ProjectFishWorks/BaseStation/Firmware/BaseStation/src/credential.h

const char* CA_cert = \
"-----BEGIN CERTIFICATE-----\n" \ 
"MIIFazCCA1OgAwIBAgIRAIIQz7DSQONZRGPgu2OCiwAwDQYJKoZIhvcNAQELBQAw\n" \
"TzELMAkGA1UEBhMCVVMxKTAnBgNVBAoTIEludGVybmV0IFNlY3VyaXR5IFJlc2Vh\n" \
"cmNoIEdyb3VwMRUwEwYDVQQDEwxJU1JHIFJvb3QgWDEwHhcNMTUwNjA0MTEwNDM4\n" \
"WhcNMzUwNjA0MTEwNDM4WjBPMQswCQYDVQQGEwJVUzEpMCcGA1UEChMgSW50ZXJu\n" \
"ZXQgU2VjdXJpdHkgUmVzZWFyY2ggR3JvdXAxFTATBgNVBAMTDElTUkcgUm9vdCBY\n" \
"MTCCAiIwDQYJKoZIhvcNAQEBBQADggIPADCCAgoCggIBAK3oJHP0FDfzm54rVygc\n" \
"h77ct984kIxuPOZXoHj3dcKi/vVqbvYATyjb3miGbESTtrFj/RQSa78f0uoxmyF+\n" \
"0TM8ukj13Xnfs7j/EvEhmkvBioZxaUpmZmyPfjxwv60pIgbz5MDmgK7iS4+3mX6U\n" \
"A5/TR5d8mUgjU+g4rk8Kb4Mu0UlXjIB0ttov0DiNewNwIRt18jA8+o+u3dpjq+sW\n" \
"T8KOEUt+zwvo/7V3LvSye0rgTBIlDHCNAymg4VMk7BPZ7hm/ELNKjD+Jo2FR3qyH\n" \
"B5T0Y3HsLuJvW5iB4YlcNHlsdu87kGJ55tukmi8mxdAQ4Q7e2RCOFvu396j3x+UC\n" \
"B5iPNgiV5+I3lg02dZ77DnKxHZu8A/lJBdiB3QW0KtZB6awBdpUKD9jf1b0SHzUv\n" \
"KBds0pjBqAlkd25HN7rOrFleaJ1/ctaJxQZBKT5ZPt0m9STJEadao0xAH0ahmbWn\n" \
"OlFuhjuefXKnEgV4We0+UXgVCwOPjdAvBbI+e0ocS3MFEvzG6uBQE3xDk3SzynTn\n" \
"jh8BCNAw1FtxNrQHusEwMFxIt4I7mKZ9YIqioymCzLq9gwQbooMDQaHWBfEbwrbw\n" \
"qHyGO0aoSCqI3Haadr8faqU9GY/rOPNk3sgrDQoo//fb4hVC1CLQJ13hef4Y53CI\n" \
"rU7m2Ys6xt0nUW7/vGT1M0NPAgMBAAGjQjBAMA4GA1UdDwEB/wQEAwIBBjAPBgNV\n" \
"HRMBAf8EBTADAQH/MB0GA1UdDgQWBBR5tFnme7bl5AFzgAiIyBpY9umbbjANBgkq\n" \
"hkiG9w0BAQsFAAOCAgEAVR9YqbyyqFDQDLHYGmkgJykIrGF1XIpu+ILlaS/V9lZL\n" \
"ubhzEFnTIZd+50xx+7LSYK05qAvqFyFWhfFQDlnrzuBZ6brJFe+GnY+EgPbk6ZGQ\n" \
"3BebYhtF8GaV0nxvwuo77x/Py9auJ/GpsMiu/X1+mvoiBOv/2X/qkSsisRcOj/KK\n" \
"NFtY2PwByVS5uCbMiogziUwthDyC3+6WVwW6LLv3xLfHTjuCvjHIInNzktHCgKQ5\n" \
"ORAzI4JMPJ+GslWYHb4phowim57iaztXOoJwTdwJx4nLCgdNbOhdjsnvzqvHu7Ur\n" \
"TkXWStAmzOVyyghqpZXjFaH3pO3JLF+l+/+sKAIuvtd7u+Nxe5AW0wdeRlN8NwdC\n" \
"jNPElpzVmbUq4JUagEiuTDkHzsxHpFKVK7q4+63SM1N95R1NbdWhscdCb+ZAJzVc\n" \
"oyi3B43njTOQ5yOf+1CceWxG1bQVs5ZufpsMljq4Ui0/1lvh+wjChP4kqKOJ2qxq\n" \
"4RgqsahDYVvTH9w7jXbyLeiNdd8XM2w9U/t7y0Ff/9yi0GE44Za4rF2LN9d11TPA\n" \
"mRGunUHBcnWEvgJBQl9nJEiU0Zsnvgc/ubhPgXRR4Xq37Z0j4r7g1SgEEzwxA57d\n" \
"emyPxgcYxn/eR44/KJ4EBs+lVDR3veyJm+kXQ99b21/+jh5Xos1AnX5iItreGCc=\n" \
"-----END CERTIFICATE-----\n";
const char* CA_cert_gmail = \
"-----BEGIN CERTIFICATE-----\n" \
"MIIFCzCCAvOgAwIBAgIQf/AFoHxM3tEArZ1mpRB7mDANBgkqhkiG9w0BAQsFADBH\n" \
"MQswCQYDVQQGEwJVUzEiMCAGA1UEChMZR29vZ2xlIFRydXN0IFNlcnZpY2VzIExM\n" \
"QzEUMBIGA1UEAxMLR1RTIFJvb3QgUjEwHhcNMjMxMjEzMDkwMDAwWhcNMjkwMjIw\n" \
"MTQwMDAwWjA7MQswCQYDVQQGEwJVUzEeMBwGA1UEChMVR29vZ2xlIFRydXN0IFNl\n" \
"cnZpY2VzMQwwCgYDVQQDEwNXUjIwggEiMA0GCSqGSIb3DQEBAQUAA4IBDwAwggEK\n" \
"AoIBAQCp/5x/RR5wqFOfytnlDd5GV1d9vI+aWqxG8YSau5HbyfsvAfuSCQAWXqAc\n" \
"+MGr+XgvSszYhaLYWTwO0xj7sfUkDSbutltkdnwUxy96zqhMt/TZCPzfhyM1IKji\n" \
"aeKMTj+xWfpgoh6zySBTGYLKNlNtYE3pAJH8do1cCA8Kwtzxc2vFE24KT3rC8gIc\n" \
"LrRjg9ox9i11MLL7q8Ju26nADrn5Z9TDJVd06wW06Y613ijNzHoU5HEDy01hLmFX\n" \
"xRmpC5iEGuh5KdmyjS//V2pm4M6rlagplmNwEmceOuHbsCFx13ye/aoXbv4r+zgX\n" \
"FNFmp6+atXDMyGOBOozAKql2N87jAgMBAAGjgf4wgfswDgYDVR0PAQH/BAQDAgGG\n" \
"MB0GA1UdJQQWMBQGCCsGAQUFBwMBBggrBgEFBQcDAjASBgNVHRMBAf8ECDAGAQH/\n" \
"AgEAMB0GA1UdDgQWBBTeGx7teRXUPjckwyG77DQ5bUKyMDAfBgNVHSMEGDAWgBTk\n" \
"rysmcRorSCeFL1JmLO/wiRNxPjA0BggrBgEFBQcBAQQoMCYwJAYIKwYBBQUHMAKG\n" \
"GGh0dHA6Ly9pLnBraS5nb29nL3IxLmNydDArBgNVHR8EJDAiMCCgHqAchhpodHRw\n" \
"Oi8vYy5wa2kuZ29vZy9yL3IxLmNybDATBgNVHSAEDDAKMAgGBmeBDAECATANBgkq\n" \
"hkiG9w0BAQsFAAOCAgEARXWL5R87RBOWGqtY8TXJbz3S0DNKhjO6V1FP7sQ02hYS\n" \
"TL8Tnw3UVOlIecAwPJQl8hr0ujKUtjNyC4XuCRElNJThb0Lbgpt7fyqaqf9/qdLe\n" \
"SiDLs/sDA7j4BwXaWZIvGEaYzq9yviQmsR4ATb0IrZNBRAq7x9UBhb+TV+PfdBJT\n" \
"DhEl05vc3ssnbrPCuTNiOcLgNeFbpwkuGcuRKnZc8d/KI4RApW//mkHgte8y0YWu\n" \
"ryUJ8GLFbsLIbjL9uNrizkqRSvOFVU6xddZIMy9vhNkSXJ/UcZhjJY1pXAprffJB\n" \
"vei7j+Qi151lRehMCofa6WBmiA4fx+FOVsV2/7R6V2nyAiIJJkEd2nSi5SnzxJrl\n" \
"Xdaqev3htytmOPvoKWa676ATL/hzfvDaQBEcXd2Ppvy+275W+DKcH0FBbX62xevG\n" \
"iza3F4ydzxl6NJ8hk8R+dDXSqv1MbRT1ybB5W0k8878XSOjvmiYTDIfyc9acxVJr\n" \
"Y/cykHipa+te1pOhv7wYPYtZ9orGBV5SGOJm4NrB3K1aJar0RfzxC3ikr7Dyc6Qw\n" \
"qDTBU39CluVIQeuQRgwG3MuSxl7zRERDRilGoKb8uY45JzmxWuKxrfwT/478JuHU\n" \
"/oTxUFqOl2stKnn7QGTq8z29W+GgBLCXSBxC9epaHM0myFH/FJlniXJfHeytWt0=\n" \
"-----END CERTIFICATE-----\n";
